import-tiago/Light-s-Thrill/Hardware/0. Project/Light's Thrill.sch

## EAGLE design Hardware/0. Project/Light's Thrill.sch (2021-03-24)

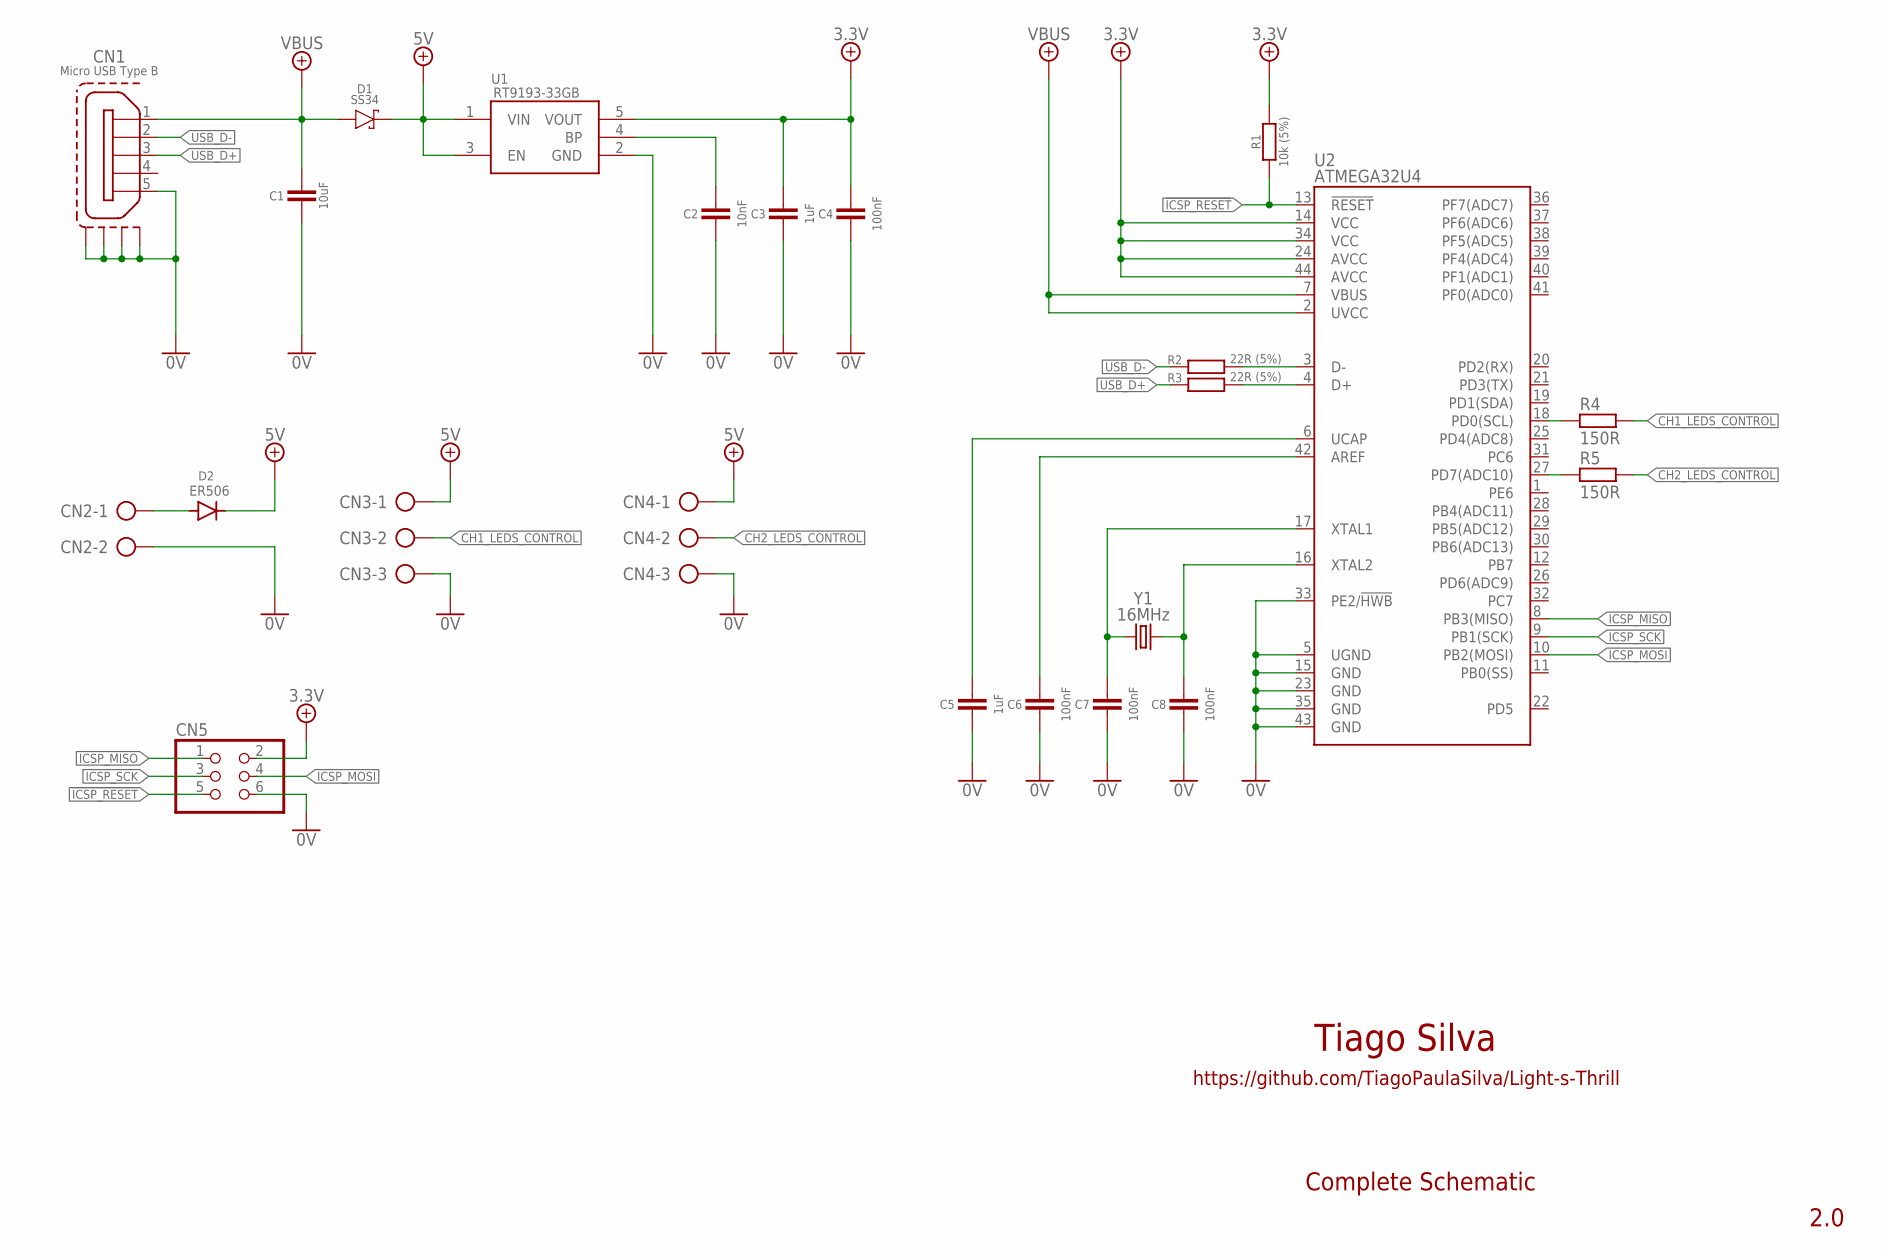
[picture p10: schematic Light's Thrill.sch]

Parts:
C1: 10uF; C0805
C2: 10nF; C0603
C3, C5: 1uF; C0603
C4, C6, C7, C8: 100nF; C0603
CN1: Micro USB Type B; 10118193-0001LF
CN2: AK500/2-H
CN3, CN4: AK500/3-H
CN5: PINHD-2X3; 2X03
D1: SS34; DO214AB
D2: ER506; DO27-15
R1: 10k (5%); R0603
R2, R3: 22R (5%); R0603
R4, R5: 150R; R0603
U1: RT9193-33GB; SOT94P279X129-5N
U2: ATMEGA32U4; TESTING_QFN-44
Y1: 16MHz; 5.0X3.2_KX-9A

Connections:
0V: C1.2, C2.2, C3.2, C4.2, C5.2, C6.2, C7.2, C8.2, CN1.5, CN1.MP1 (S1), CN1.MP2 (S2), CN1.MP3 (S3), CN1.MP4 (S4), CN2.2, CN3.3, CN4.3, CN5.6, U1.2 (GND), U2.5 (UGND), U2.15 (GND), U2.23 (GND), U2.33 (PE2/!HWB), U2.35 (GND), U2.43 (GND)
3.3V: C3.1, C4.1, CN5.2, R1.2, U1.5 (VOUT), U2.14 (VCC), U2.24 (AVCC), U2.34 (VCC), U2.44 (AVCC)
5V: CN3.1, CN4.1, D1.C (K), D2.C, U1.1 (VIN), U1.3 (EN)
!ICSP_RESET: CN5.5, R1.1, U2.13 (!RESET)
CH1_LEDS_CONTROL: CN3.2, R4.2
CH2_LEDS_CONTROL: CN4.2, R5.2
ICSP_MISO: CN5.1, U2.8 (PB3(MISO))
ICSP_MOSI: CN5.4, U2.10 (PB2(MOSI))
ICSP_SCK: CN5.3, U2.9 (PB1(SCK))
unnamed: R4.1, U2.18 (PD0(SCL))
unnamed: CN2.1, D2.A
unnamed: R5.1, U2.27 (PD7(ADC10))
unnamed: R3.2, U2.4 (D+)
unnamed: C7.1, U2.17 (XTAL1), Y1.1
unnamed: C8.1, U2.16 (XTAL2), Y1.3 (2)
unnamed: C5.1, U2.6 (UCAP)
unnamed: C6.1, U2.42 (AREF)
unnamed: R2.2, U2.3 (D-)
unnamed: C2.1, U1.4 (BP)
USB_D+: CN1.3, R3.1
USB_D-: CN1.2, R2.1
VBUS: C1.1, CN1.1, D1.A, U2.2 (UVCC), U2.7 (VBUS)

Notes on the sheet:
Tiago Silva
https://github.com/TiagoPaulaSilva/Light-s-Thrill
2.0
Complete Schematic
